ricardoquesada/unijoysticle/client_ios/src/raw/screenshot2-5.5.png

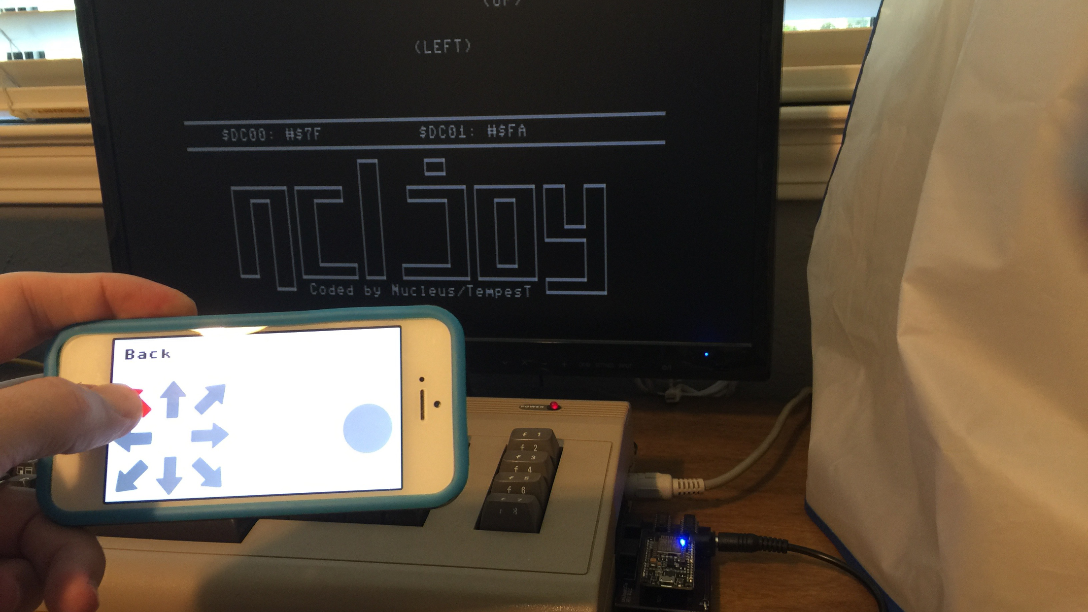
client_ios/src/raw/screenshot2-5.5.png
