ricardoquesada/unijoysticle/client_ios/src/raw/screenshot1-5.5.png

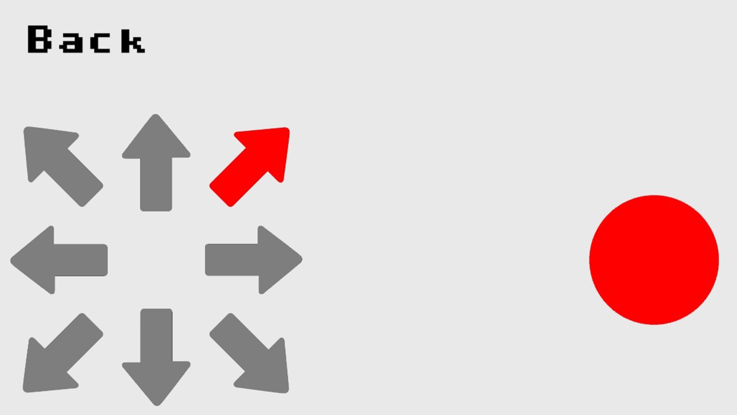
client_ios/src/raw/screenshot1-5.5.png
