ricardoquesada/unijoysticle/client_ios/src/raw/screenshot3-5.5.png

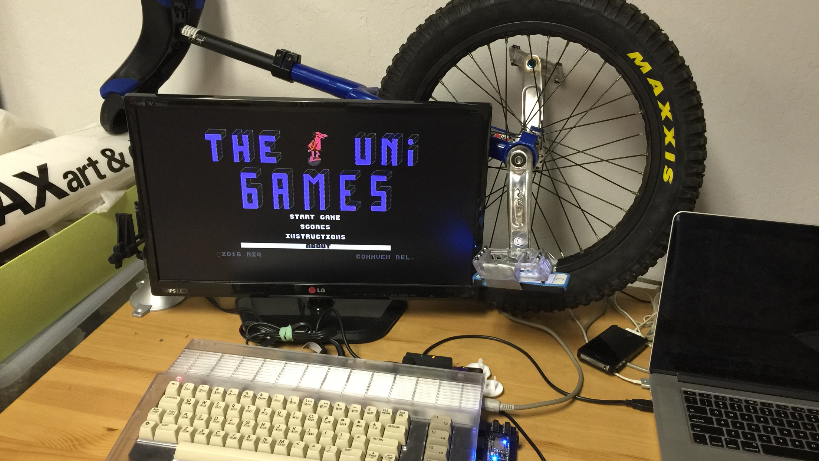
client_ios/src/raw/screenshot3-5.5.png
