ricardoquesada/unijoysticle/client_ios/src/raw/screenshot4-5.5.png

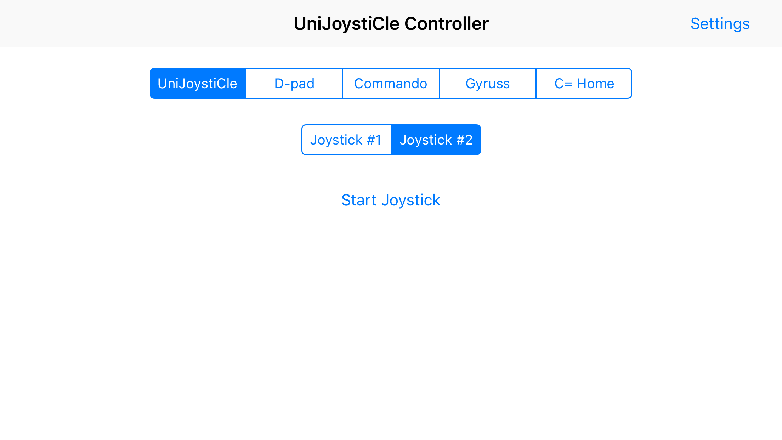
client_ios/src/raw/screenshot4-5.5.png
